kpmquockhanh/status-cube-watch/docs/superpowers/plans/2026-10-02-pomodoro-portal-ota.md

# Pomodoro card, WiFi config portal and OTA: implementation plan

> **For agentic workers:** REQUIRED SUB-SKILL: Use superpowers:subagent-driven-development (recommended) or superpowers:executing-plans to implement this plan task-by-task. Steps use checkbox (`- [ ]`) syntax for tracking.

**Goal:** Make the cube a standalone desk device: change WiFi and bridge settings from a captive portal, flash it over WiFi, and run a Pomodoro timer on it from a dedicated touch-controlled card.

**Architecture:** A new `settings` module (NVS over `config.h` defaults) feeds `net.cpp`, a blocking `portal` module (SoftAP + DNS catch-all + one-page form) and `ota` (ArduinoOTA). The Pomodoro is a pure state machine (`pomodoro.cpp`) plus a pure gesture classifier (`gesture.cpp`), both host-tested. The Pomodoro card is a virtual last card in the deck, drawn by `ui.cpp` through the existing gauge-card renderer (extended with a `RingStyle`). The bridge and payload contract are untouched.

**Tech Stack:** PlatformIO / Arduino-ESP32, LovyanGFX, ArduinoJson, `Preferences` (NVS), `WebServer` + `DNSServer`, `ArduinoOTA`; desktop sim (SDL2, `make`); plain `c++ -std=c++17` host tests.

**Spec:** `docs/superpowers/specs/2026-10-02-pomodoro-portal-ota-design.md`

## Global Constraints

- Firmware stays within C++11 (arduino-esp32's default): no default member initializers in types that are brace-initialized as aggregates, no C++14 library features. The sim and host tests build as C++17.
- Code shared with the simulator (`main.cpp`, `ui.cpp`, `payload.cpp`, `pomodoro.cpp`, `gesture.cpp`) may only use what `firmware/sim/Arduino.h` provides (`millis`, `delay`, `Serial`, `min`/`max`/`constrain`, `<cstring>`). Hardware-only code (`settings.cpp`, `portal.cpp`, `ota.cpp`) gets a sim stand-in in `firmware/sim/`.
- `pomodoro.cpp` and `gesture.cpp` take time as an argument and include no Arduino header, so host tests can build them.
- Settings precedence: NVS value if the key exists, else the `config.h` default. An empty NVS plus a working `config.h` must behave exactly as before.
- Names are fixed by the spec: OTA hostname `claude-cube`; portal AP `claude-cube-XXXX` (last two MAC bytes, upper-case hex), open, address `192.168.4.1`; NVS namespace `cube` with keys `ssid`, `pass`, `bridge`, `otapass`.
- Timings: WiFi join timeout 20 s (80 x 250 ms); boot hold for the portal 5000 ms; portal idle auto-retry 60 s; long-press 600 ms; reset-press 2000 ms; OTA/Pomodoro config constants as below.
- Pomodoro constants live in `config.h`: `POMO_FOCUS_MIN` 25, `POMO_BREAK_MIN` 5, `POMO_LONG_MIN` 15, `POMO_SESSIONS` 4. Minutes must be 1..99 and sessions 1..9 (compile-time `static_assert`). Defaults are also provided in `main.cpp` so an old `config.h` still builds.
- The Pomodoro card is the only card whose text the firmware formats (`MM:SS`). It is not in the payload, not counted against `MAX_CARDS`, and `payload.h/.cpp`, `bridge/cards.mjs` and the payload contract do not change.
- `firmware/src/config.h` is gitignored and holds real credentials: edit it only to add the new constants, never print or commit its secrets.
- This directory is **not a git repository**. Every "Commit" step below is conditional: if `git rev-parse --is-inside-work-tree` succeeds, commit; if not, skip the step (do not run `git init` unless the user asks). Commit messages end with the attribution trailer given in the session's system reminder.
- Verification commands (run from the repo root unless a `cd` is shown):
  - host tests: `cd firmware/sim && make test`
  - firmware build: `cd firmware && pio run`
  - sim build: `cd firmware/sim && make`
  - screenshots: `cd firmware/sim && make build/cube-shot && ./build/cube-shot build/shot @<view>`; open the PNG with the Read tool to look at it.

## Review Focus

Failure modes the spec implies but a straight implementation would not test. Each has a test in the task that owns the code.

1. **A long-press must not also fire a tap or swipe when the finger lifts, and a hold on a non-Pomodoro card must still be ignored on release** (Task 8: `gesture_test`).
2. **A phase must end correctly when `tick` is not called for a long time (a blocked HTTP fetch, a long gap), and when the pause press lands exactly at the end of a phase** (Task 7: `pomodoro_test`).
3. **`millis()` wraparound (about every 49 days) must not corrupt the timer or the gesture timing** (Task 7 and Task 8).
4. **Portal form safety: an SSID or bridge URL containing `"`, `<`, `&` must not break the form; a blank password keeps the stored one only while the SSID is unchanged; bridge URLs with spaces or a non-`http://` scheme are refused** (Task 1: `portal_util_test`).
5. **Bridge unreachable (WiFi fine): the deck must still contain the Pomodoro card, the timer must stay correct, and the alert must still fire** (Task 9: empty-payload shot; Task 10: manual check with a dead `BRIDGE_URL`).

---

### Task 1: Host-test harness and portal helpers

**Files:**
- Create: `firmware/sim/tests/check.h`
- Create: `firmware/sim/tests/portal_util_test.cpp`
- Create: `firmware/src/portal_util.h`
- Modify: `firmware/sim/Makefile`

**Interfaces:**
- Produces (used by Task 4): in `portal_util.h`, all `inline`, namespace-free, taking `std::string`:
  - `bool portalValidSsid(const std::string&)`: 1..32 bytes
  - `bool portalValidBridgeUrl(const std::string&)`: `http://` + non-empty host, <= 127 bytes, no whitespace
  - `std::string portalHtmlEscape(const std::string&)`
  - `std::string portalTrim(const std::string&)`
  - `std::string portalResolvePassword(oldSsid, newSsid, oldPass, newPass)`: new if non-empty; else old only when the SSID is unchanged; else empty
  - `std::string portalKeepIfBlank(old, neu)`: `neu` unless blank, then `old`
- Produces (used by Tasks 7, 8): `check.h` with `CHECK(cond)` and `int checksDone(const char *name)`; the Makefile `test` target and `TESTS` list.

- [ ] **Step 1: Write the test helper**

Create `firmware/sim/tests/check.h`:

```cpp
#pragma once
// Tiny assertion helper for the host-side tests: no framework, one include.
#include <cstdio>

static int g_checks = 0;
static int g_failed = 0;

#define CHECK(cond)                                                          \
  do {                                                                       \
    g_checks++;                                                              \
    if (!(cond)) {                                                           \
      g_failed++;                                                            \
      std::printf("  FAIL %s:%d  %s\n", __FILE__, __LINE__, #cond);          \
    }                                                                        \
  } while (0)

// Prints the summary line and returns the process exit code.
static int checksDone(const char *name) {
  std::printf("%s: %d checks, %d failed\n", name, g_checks, g_failed);
  return g_failed ? 1 : 0;
}
```

- [ ] **Step 2: Write the failing test**

Create `firmware/sim/tests/portal_util_test.cpp`:

```cpp
#include <string>

#include "check.h"
#include "portal_util.h"

namespace {

void testSsid() {
  CHECK(!portalValidSsid(""));
  CHECK(portalValidSsid("a"));
  CHECK(portalValidSsid(std::string(32, 'x')));
  CHECK(!portalValidSsid(std::string(33, 'x')));
}

void testBridgeUrl() {
  CHECK(portalValidBridgeUrl("http://192.168.1.50:8787/api/status"));
  CHECK(portalValidBridgeUrl("http://host"));
  CHECK(portalValidBridgeUrl("http://" + std::string(120, 'a')));   // 127 bytes
  CHECK(!portalValidBridgeUrl("http://" + std::string(121, 'a')));  // 128 bytes
  CHECK(!portalValidBridgeUrl(""));
  CHECK(!portalValidBridgeUrl("http://"));
  CHECK(!portalValidBridgeUrl("http://:8787/x"));
  CHECK(!portalValidBridgeUrl("http:///x"));
  CHECK(!portalValidBridgeUrl("https://host/x"));  // the bridge is plain HTTP
  CHECK(!portalValidBridgeUrl("ftp://host"));
  CHECK(!portalValidBridgeUrl("http://bad host/"));
  CHECK(!portalValidBridgeUrl("http://host/\n"));
  CHECK(!portalValidBridgeUrl("192.168.1.50:8787"));
}

void testEscape() {
  CHECK(portalHtmlEscape("plain") == "plain");
  CHECK(portalHtmlEscape("a\"b") == "a&quot;b");
  CHECK(portalHtmlEscape("<script>") == "&lt;script&gt;");
  CHECK(portalHtmlEscape("Tom & Jerry's") == "Tom &amp; Jerry&#39;s");
  CHECK(portalHtmlEscape("\"><img src=x>") == "&quot;&gt;&lt;img src=x&gt;");
  CHECK(portalHtmlEscape("") == "");
}

void testTrim() {
  CHECK(portalTrim("  http://h/ \r\n") == "http://h/");
  CHECK(portalTrim("x") == "x");
  CHECK(portalTrim("   ") == "");
  CHECK(portalTrim("") == "");
  CHECK(portalTrim(" a b ") == "a b");
}

void testPassword() {
  // A typed password always wins.
  CHECK(portalResolvePassword("home", "home", "old", "new") == "new");
  CHECK(portalResolvePassword("home", "other", "old", "new") == "new");
  // Blank keeps the stored one, but only for the same network.
  CHECK(portalResolvePassword("home", "home", "old", "") == "old");
  // A different network with a blank password is an open network.
  CHECK(portalResolvePassword("home", "cafe", "old", "") == "");
  // No stored password and a blank field stays blank.
  CHECK(portalResolvePassword("", "home", "", "") == "");
}

void testKeepIfBlank() {
  CHECK(portalKeepIfBlank("old", "") == "old");
  CHECK(portalKeepIfBlank("old", "new") == "new");
  CHECK(portalKeepIfBlank("", "") == "");
}

}  // namespace

int main() {
  testSsid();
  testBridgeUrl();
  testEscape();
  testTrim();
  testPassword();
  testKeepIfBlank();
  return checksDone("portal_util_test");
}
```

- [ ] **Step 3: Add the test target to the Makefile**

In `firmware/sim/Makefile`, replace the `.PHONY` line and add the test rules just above `clean:`. Use Edit with:

old:
```make
clean:
	rm -rf build

.PHONY: all run shot clean
```
new:
```make
# Host-side unit tests for the logic that has no hardware in it. A plain
# compiler: no SDL, LovyanGFX or Arduino. Each test links only the sources it
# is given an extra rule for below.
TESTS := build/portal_util_test

build/%_test: tests/%_test.cpp
	@mkdir -p build
	$(CXX) -std=c++17 -Wall -Wextra -I../src -Itests $(filter %.cpp,$^) -o $@

test: $(TESTS)
	@for t in $(TESTS); do ./$$t || exit 1; done

clean:
	rm -rf build

.PHONY: all run shot test clean
```

- [ ] **Step 4: Run it to verify it fails**

Run: `cd firmware/sim && make test`
Expected: FAIL to compile with `'portal_util.h' file not found`.

- [ ] **Step 5: Write the helpers**

Create `firmware/src/portal_util.h`:

```cpp
#pragma once
// Pure helpers for the setup portal. No Arduino or WiFi includes, so the host
// tests in sim/tests can build this with a plain compiler.
#include <string>

// SSIDs are 1..32 bytes. WPA passphrases are 8..63, but an open network has
// none, so the password is only length-checked where it is stored.
inline bool portalValidSsid(const std::string &s) { return !s.empty() && s.size() <= 32; }

// The bridge speaks plain HTTP on the LAN (see net.cpp). Anything else would
// only surface later as a confusing "bad BRIDGE_URL" on the display.
inline bool portalValidBridgeUrl(const std::string &u) {
  static const std::string scheme = "http://";
  if (u.size() > 127 || u.compare(0, scheme.size(), scheme) != 0) return false;
  if (u.find_first_of(" \t\r\n") != std::string::npos) return false;
  const std::string rest = u.substr(scheme.size());
  return !rest.empty() && rest[0] != ':' && rest[0] != '/';
}

// Values go back into the form as value="...", so a quote in an SSID must not
// end the attribute and a "<" must not start a tag.
inline std::string portalHtmlEscape(const std::string &in) {
  std::string out;
  out.reserve(in.size());
  for (char c : in) {
    switch (c) {
      case '&': out += "&amp;"; break;
      case '<': out += "&lt;"; break;
      case '>': out += "&gt;"; break;
      case '"': out += "&quot;"; break;
      case '\'': out += "&#39;"; break;
      default: out += c;
    }
  }
  return out;
}

inline std::string portalTrim(const std::string &s) {
  const char *ws = " \t\r\n";
  const size_t a = s.find_first_not_of(ws);
  if (a == std::string::npos) return std::string();
  return s.substr(a, s.find_last_not_of(ws) - a + 1);
}

// A blank password field means "keep what is stored", but only while the SSID
// is unchanged. Pointing the cube at a different network with a blank
// password means an open network, not the old network's password.
inline std::string portalResolvePassword(const std::string &oldSsid, const std::string &newSsid,
                                         const std::string &oldPass, const std::string &newPass) {
  if (!newPass.empty()) return newPass;
  return oldSsid == newSsid ? oldPass : std::string();
}

inline std::string portalKeepIfBlank(const std::string &oldValue, const std::string &newValue) {
  return newValue.empty() ? oldValue : newValue;
}
```

- [ ] **Step 6: Run the test to verify it passes**

Run: `cd firmware/sim && make test`
Expected: `portal_util_test: 33 checks, 0 failed` (the count may differ by a few; the point is `0 failed` and exit status 0).

- [ ] **Step 7: Commit (only if inside a git repo)**

```bash
git add firmware/sim/tests firmware/sim/Makefile firmware/src/portal_util.h
git commit -m "test: host-side test harness and portal helpers"
```

---

### Task 2: Settings (NVS) and the network layer

**Files:**
- Create: `firmware/src/settings.h`
- Create: `firmware/src/settings.cpp`
- Create: `firmware/sim/settings_sim.cpp`
- Modify: `firmware/src/net.h`, `firmware/src/net.cpp`, `firmware/sim/net_sim.cpp`
- Modify: `firmware/src/main.cpp`, `firmware/sim/Makefile`, `firmware/src/config.h.example`

**Interfaces:**
- Produces (used by Tasks 4, 5):
  - `struct Settings { char ssid[33]; char pass[64]; char bridge[128]; char otaPass[64]; }`
  - `void settingsLoad()`: call once at boot
  - `const Settings &settings()`
  - `bool settingsSave(const Settings &s)`: writes NVS and updates the in-memory copy; the caller reboots
  - `bool settingsHaveWifi()`
  - `bool netBegin()` (was `void`): `false` if not connected after about 20 s

- [ ] **Step 1: Write `settings.h`**

```cpp
#pragma once
#include <stddef.h>
#include <stdint.h>

// Everything the setup portal can change. Stored in NVS; any key that was
// never stored falls back to config.h, so a freshly flashed cube behaves
// exactly as it did before the portal existed.
struct Settings {
  char ssid[33];     // WiFi SSID, up to 32 bytes
  char pass[64];     // WPA passphrase, up to 63 bytes; empty = open network
  char bridge[128];  // bridge URL, up to 127 bytes
  char otaPass[64];  // ArduinoOTA password; empty = none
};

void settingsLoad();  // call once at boot, before anything reads settings()
const Settings &settings();
// Persists `s` and makes it the current settings. The caller reboots.
bool settingsSave(const Settings &s);
// True when there is any SSID to join, from NVS or from config.h.
bool settingsHaveWifi();
```

- [ ] **Step 2: Write `settings.cpp`**

```cpp
#include "settings.h"

#include <Arduino.h>
#include <Preferences.h>

#include "config.h"

#ifndef OTA_PASSWORD
#define OTA_PASSWORD ""
#endif

namespace {

constexpr char NS[] = "cube";
Settings g_settings;

void loadKey(Preferences &p, const char *key, char *dst, size_t cap, const char *fallback) {
  if (p.isKey(key)) {
    p.getString(key, dst, cap);
  } else {
    strlcpy(dst, fallback, cap);
  }
}

void useDefaults() {
  strlcpy(g_settings.ssid, WIFI_SSID, sizeof(g_settings.ssid));
  strlcpy(g_settings.pass, WIFI_PASSWORD, sizeof(g_settings.pass));
  strlcpy(g_settings.bridge, BRIDGE_URL, sizeof(g_settings.bridge));
  strlcpy(g_settings.otaPass, OTA_PASSWORD, sizeof(g_settings.otaPass));
}

}  // namespace

void settingsLoad() {
  Preferences p;
  // Read-write even though we only read: a read-only open of a namespace that
  // does not exist yet fails and logs an error on every first boot.
  if (!p.begin(NS, false)) {
    Serial.println("[settings] NVS unavailable -- using config.h");
    useDefaults();
    return;
  }
  loadKey(p, "ssid", g_settings.ssid, sizeof(g_settings.ssid), WIFI_SSID);
  loadKey(p, "pass", g_settings.pass, sizeof(g_settings.pass), WIFI_PASSWORD);
  loadKey(p, "bridge", g_settings.bridge, sizeof(g_settings.bridge), BRIDGE_URL);
  loadKey(p, "otapass", g_settings.otaPass, sizeof(g_settings.otaPass), OTA_PASSWORD);
  p.end();
}

const Settings &settings() { return g_settings; }

bool settingsSave(const Settings &s) {
  Preferences p;
  if (!p.begin(NS, false)) return false;
  // putString returns the byte count, which is 0 for an empty string even on
  // success, so success here just means the namespace opened. An empty value
  // is stored on purpose: a blank password means "open network", not "use the
  // config.h one".
  p.putString("ssid", s.ssid);
  p.putString("pass", s.pass);
  p.putString("bridge", s.bridge);
  p.putString("otapass", s.otaPass);
  p.end();
  g_settings = s;
  return true;
}

bool settingsHaveWifi() { return g_settings.ssid[0] != '\0'; }
```

- [ ] **Step 3: Write the sim stand-in `firmware/sim/settings_sim.cpp`**

```cpp
// Desktop stand-in for settings.cpp: a laptop has no NVS, so the simulator
// always runs on the config.h defaults and saving is a no-op.

#include <Arduino.h>

#include "../src/config.h"
#include "../src/settings.h"

#ifndef OTA_PASSWORD
#define OTA_PASSWORD ""
#endif

namespace {
Settings g_settings;
}

void settingsLoad() {
  strlcpy(g_settings.ssid, WIFI_SSID, sizeof(g_settings.ssid));
  strlcpy(g_settings.pass, WIFI_PASSWORD, sizeof(g_settings.pass));
  strlcpy(g_settings.bridge, BRIDGE_URL, sizeof(g_settings.bridge));
  strlcpy(g_settings.otaPass, OTA_PASSWORD, sizeof(g_settings.otaPass));
}

const Settings &settings() { return g_settings; }

bool settingsSave(const Settings &s) {
  g_settings = s;
  Serial.println("[settings] (sim) not persisted");
  return true;
}

bool settingsHaveWifi() { return g_settings.ssid[0] != '\0'; }
```

- [ ] **Step 4: Make `net` read from settings**

`firmware/src/net.h`: change `void netBegin();` to:

```cpp
// Joins the stored network. Returns false if it is still not connected after
// about 20 s, so the caller can fall back to the setup portal.
bool netBegin();
```

`firmware/src/net.cpp`: replace `#include "config.h"` with `#include "settings.h"`. Replace the whole `netBegin` function with:

```cpp
bool netBegin() {
  WiFi.mode(WIFI_STA);
  WiFi.setSleep(true);  // the radio idles between 5s polls
  const Settings &s = settings();
  // A null passphrase is how the WiFi library spells "open network".
  WiFi.begin(s.ssid, s.pass[0] ? s.pass : nullptr);
  Serial.printf("[net] connecting to %s", s.ssid);
  for (int i = 0; i < 80 && WiFi.status() != WL_CONNECTED; i++) {
    delay(250);
    Serial.print('.');
  }
  Serial.println();
  if (WiFi.status() == WL_CONNECTED) {
    Serial.printf("[net] %s  rssi %d\n", WiFi.localIP().toString().c_str(), WiFi.RSSI());
    return true;
  }
  fail("wifi timeout");
  Serial.println("[net] could not join");
  return false;
}
```

and change `http.begin(BRIDGE_URL)` to `http.begin(settings().bridge)`.

`firmware/sim/net_sim.cpp`: change `void netBegin() {` to `bool netBegin() {` and add `return true;` as its last line:

```cpp
bool netBegin() {
  Serial.printf("[net] simulator -> %s\n", bridgeUrl().c_str());
  return true;
}
```

- [ ] **Step 5: Use settings in `main.cpp`**

Edits in `firmware/src/main.cpp`:
1. After `#include "payload.h"` add `#include "settings.h"`.
2. In `setup()`, after `Serial.println("\n[boot] claude-status-cube");` add `settingsLoad();`.
3. Replace `uiMessage(lcd, "CONNECTING", WIFI_SSID);` with `uiMessage(lcd, "CONNECTING", settings().ssid);`.

(`netBegin();` stays as a bare call for now; Task 4 uses its result.)

- [ ] **Step 6: Wire the sim Makefile and document the config**

In `firmware/sim/Makefile` change:

```make
SRCS := ../src/main.cpp ../src/ui.cpp ../src/payload.cpp \
        net_sim.cpp touch_sim.cpp sdl_main.cpp
```
to:
```make
SRCS := ../src/main.cpp ../src/ui.cpp ../src/payload.cpp \
        net_sim.cpp touch_sim.cpp settings_sim.cpp sdl_main.cpp
```

Append to `firmware/src/config.h.example`:

```c
// Optional: default OTA password. The setup portal can set or change it; with
// neither, OTA still works but anyone on the network can flash the cube.
// #define OTA_PASSWORD  "choose-one"
```

- [ ] **Step 7: Build everything**

Run: `cd firmware && pio run`
Expected: `[SUCCESS]`.

Run: `cd firmware/sim && make`
Expected: `built build/cube-sim` with no errors.

Behaviour is unchanged at this point: with an empty NVS, `settings()` returns the `config.h` values.

- [ ] **Step 8: Commit (only if inside a git repo)**

```bash
git add firmware/src firmware/sim
git commit -m "feat(firmware): NVS-backed settings with config.h fallback"
```

---
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
