kpmquockhanh/status-cube-watch/firmware/src/readings_key.h

#pragma once
// What the cards read, folded into one number, for screen sleep: main.cpp
// counts a payload as activity (idle_sleep.h) only when its key differs from
// the last one's. "A payload arrived" is not enough: the Mac resends the same
// payload every 5 s and the bridge rebuilds it for every WiFi poll, so the
// screen would stay on for as long as the link is up. Pure, so it is
// host-tested.
//
// In the key: the card count, titles, every gauge, the mail badge, and a text
// card's value (spend, tokens, model), which move only when Claude is used.
// Left out: a ring card's value, which is the reset countdown, and every
// sub-line and legend row, which carry countdowns, projections and "active 3m
// ago". All of those change with the clock alone and would keep the screen
// awake. Accents follow the gauges, so they add nothing.

#include <stddef.h>
#include <stdint.h>

#include "payload.h"

namespace readings_detail {
inline uint32_t mix(uint32_t h, uint8_t b) { return (h ^ b) * 16777619u; }  // FNV-1a

inline uint32_t mixStr(uint32_t h, const char *s, size_t cap) {
  for (size_t i = 0; i < cap && s[i]; i++) h = mix(h, (uint8_t)s[i]);
  return mix(h, 0);  // so "AB" + "C" and "A" + "BC" differ
}
}  // namespace readings_detail

inline uint32_t readingsKey(const Payload &p) {
  using namespace readings_detail;
  uint32_t h = 2166136261u;
  h = mix(h, p.valid);
  h = mix(h, p.nCards);
  for (uint8_t i = 0; i < p.nCards && i < MAX_CARDS; i++) {
    const Card &c = p.cards[i];
    h = mixStr(h, c.title, sizeof(c.title));
    h = mix(h, (uint8_t)c.gauge);
    h = mix(h, (uint8_t)c.gauge2);
    if (c.gauge == GAUGE_NONE) h = mixStr(h, c.value, sizeof(c.value));
    h = mixStr(h, c.mail, sizeof(c.mail));
  }
  return h;
}
