kpmquockhanh/status-cube-watch/firmware/src/portal_util.h

#pragma once
// Pure helpers for the setup portal. No Arduino or WiFi includes, so the host
// tests in sim/tests can build this with a plain compiler.
#include <string>

// Reboot into the normal boot flow only when a Mac becomes bonded while the
// portal is up. An already-bonded cube reaching the portal (boot-time hold) must
// stay there so it can use "Forget paired Mac".
inline bool portalBondedTransition(bool bondedAtStart, bool bondedNow) { return !bondedAtStart && bondedNow; }

// The portal runs AP+STA, so the station side can rejoin the saved network
// while the form is up. A join that fails makes the radio scan every channel,
// and the SoftAP has to follow it, which knocks a phone off the form and starves
// a Bluetooth pairing. So the core's auto-reconnect is off in the portal, and
// this decides when to make one bounded attempt: only while `quiet` (no phone on
// the AP, no Mac pairing), at most ATTEMPT_MS long, one every
// EVERY_MS. A joined station is never stopped: it stays on one channel and does
// not disturb the AP. Unsigned arithmetic: correct across a millis() wrap.
enum class PortalStaAction : unsigned char { None, Begin, Stop };

class PortalSta {
 public:
  static constexpr unsigned long ATTEMPT_MS = 10000;  // a join plus DHCP
  static constexpr unsigned long EVERY_MS = 30000;    // from one attempt's start to the next

  // `tryNow`: the first attempt may start at once (the portal was asked for),
  // else a full period from now (a join has just failed).
  void begin(unsigned long now, bool tryNow) {
    _trying = false;
    _up = false;
    _start = tryNow ? now - EVERY_MS : now;
  }

  PortalStaAction update(unsigned long now, bool haveSsid, bool quiet, bool staUp) {
    if (staUp) {
      _up = true;
      _trying = false;
      return PortalStaAction::None;
    }
    if (_up) {  // the link dropped: try again as soon as it is quiet
      _up = false;
      _start = now - EVERY_MS;
    }
    if (_trying) {
      if (quiet && now - _start < ATTEMPT_MS) return PortalStaAction::None;
      _trying = false;
      return PortalStaAction::Stop;
    }
    if (!haveSsid || !quiet || now - _start < EVERY_MS) return PortalStaAction::None;
    _trying = true;
    _start = now;
    return PortalStaAction::Begin;
  }

 private:
  bool _trying = false;
  bool _up = false;
  unsigned long _start = 0;
};

// A cube that reached the portal only because its WiFi was down goes back to
// the normal boot flow as soon as the saved network is joined, but never while
// someone is using the form or a Mac is pairing.
inline bool portalStaRecoveredReboot(bool autoRetry, bool staUp, bool phoneOnAp, bool bleBusy) {
  return autoRetry && staUp && !phoneOnAp && !bleBusy;
}

// With AP+STA the form is also reachable from the LAN. A request must name the
// cube by the address it arrived on (a DNS-rebinding page names its own host)
// and a POST must carry the token that only the served form holds (another
// page on the LAN cannot read it, so it cannot forge a save or a forget).
inline bool portalHostIs(const std::string &host, const std::string &ip) {
  return host == ip || host == ip + ":80";
}

inline bool portalTokenOk(const std::string &sent, const std::string &token) {
  return !token.empty() && sent == token;
}

// SSIDs are 1..32 bytes. WPA passphrases are 8..63, but an open network has
// none, so the password is only length-checked where it is stored.
inline bool portalValidSsid(const std::string &s) { return !s.empty() && s.size() <= 32; }

// WPA passphrases are 8..63 characters; WiFi.begin rejects anything shorter, so
// storing one would leave the cube retrying a join that cannot succeed. Empty
// means an open network.
inline bool portalValidWifiPassword(const std::string &p) {
  return p.empty() || (p.size() >= 8 && p.size() <= 63);
}

// The bridge speaks plain HTTP on the LAN (see net.cpp). Anything else would
// only surface later as a confusing "bad BRIDGE_URL" on the display.
inline bool portalValidBridgeUrl(const std::string &u) {
  static const std::string scheme = "http://";
  if (u.size() > 127 || u.compare(0, scheme.size(), scheme) != 0) return false;
  if (u.find_first_of(" \t\r\n") != std::string::npos) return false;
  const std::string rest = u.substr(scheme.size());
  return !rest.empty() && rest[0] != ':' && rest[0] != '/';
}

// Values go back into the form as value="...", so a quote in an SSID must not
// end the attribute and a "<" must not start a tag.
inline std::string portalHtmlEscape(const std::string &in) {
  std::string out;
  out.reserve(in.size());
  for (char c : in) {
    switch (c) {
      case '&': out += "&amp;"; break;
      case '<': out += "&lt;"; break;
      case '>': out += "&gt;"; break;
      case '"': out += "&quot;"; break;
      case '\'': out += "&#39;"; break;
      default: out += c;
    }
  }
  return out;
}

inline std::string portalTrim(const std::string &s) {
  const char *ws = " \t\r\n";
  const size_t a = s.find_first_not_of(ws);
  if (a == std::string::npos) return std::string();
  return s.substr(a, s.find_last_not_of(ws) - a + 1);
}

// A blank password field means "keep what is stored", but only while the SSID
// is unchanged. Pointing the cube at a different network with a blank
// password means an open network, not the old network's password.
inline std::string portalResolvePassword(const std::string &oldSsid, const std::string &newSsid,
                                         const std::string &oldPass, const std::string &newPass) {
  if (!newPass.empty()) return newPass;
  return oldSsid == newSsid ? oldPass : std::string();
}

inline std::string portalKeepIfBlank(const std::string &oldValue, const std::string &newValue) {
  return newValue.empty() ? oldValue : newValue;
}

// A blank OTA password field keeps the stored one, so clearing it takes the
// form's "remove" box.
inline std::string portalOtaPassword(const std::string &oldPass, const std::string &typed, bool clear) {
  return clear ? std::string() : portalKeepIfBlank(oldPass, typed);
}

// Parses a whole-string decimal integer in [lo, hi]. A blank field keeps
// `keep`; anything else (letters, trailing junk, out of range) is rejected.
inline bool portalParseInt(const std::string &raw, int lo, int hi, int keep, int &out) {
  const std::string t = portalTrim(raw);
  if (t.empty()) { out = keep; return true; }
  if (t.size() > 4) return false;
  int v = 0;
  for (char c : t) {
    if (c < '0' || c > '9') return false;
    v = v * 10 + (c - '0');
  }
  if (v < lo || v > hi) return false;
  out = v;
  return true;
}
