kpmquockhanh/status-cube-watch/firmware/sim/Arduino.h

#pragma once
// Just enough of the Arduino core for the desktop simulator.
//
// This is deliberately tiny: the firmware sources only reach for millis(),
// delay(), Serial logging and the clamp helpers. Everything here is an inline
// function rather than a macro so it cannot collide with <algorithm> or with
// LovyanGFX's own templates.

#include <chrono>
#include <cstdarg>
#include <cstdint>
#include <cstdlib>
#include <cstdio>
#include <cstring>
#include <thread>

#ifdef SIM_VIRTUAL_CLOCK
// `make bench`: time is a counter that sim/bench.cpp advances. A ten-minute
// scenario runs in about a second, and every run gives the same result. A
// delay is booked as time the CPU spends idle, at the clock it was set to.
extern uint64_t g_simUs;
void simDelayUs(uint64_t us);
void simSetCpuMhz(uint32_t mhz);
inline uint32_t millis() { return (uint32_t)(g_simUs / 1000); }
inline void delay(uint32_t ms) { simDelayUs(ms * 1000ull); }
inline bool setCpuFrequencyMhz(uint32_t mhz) {
  simSetCpuMhz(mhz);
  return true;
}
#else
inline uint32_t millis() {
  using namespace std::chrono;
  static const auto t0 = steady_clock::now();
  return (uint32_t)duration_cast<milliseconds>(steady_clock::now() - t0).count();
}

inline void delay(uint32_t ms) { std::this_thread::sleep_for(std::chrono::milliseconds(ms)); }
inline bool setCpuFrequencyMhz(uint32_t) { return true; }  // no-op on the desktop
#endif

struct EspShim {
  [[noreturn]] void restart() { std::printf("[esp] restart requested (sim exits)\n"); std::exit(0); }
};
inline EspShim ESP;

inline int max(int a, int b) { return a > b ? a : b; }
inline int min(int a, int b) { return a < b ? a : b; }
inline int constrain(int v, int lo, int hi) { return v < lo ? lo : (v > hi ? hi : v); }

// Serial goes to the terminal, so the simulator prints the same boot and
// fetch diagnostics you would see over USB.
struct SerialShim {
  void begin(unsigned long) {}
  void print(char c) { fputc(c, stdout); fflush(stdout); }
  void print(const char *s) { fputs(s, stdout); fflush(stdout); }
  void println() { fputc('\n', stdout); }
  void println(const char *s) { printf("%s\n", s); }
  int printf(const char *fmt, ...) {
    va_list ap;
    va_start(ap, fmt);
    const int n = vfprintf(stdout, fmt, ap);
    va_end(ap);
    fflush(stdout);
    return n;
  }
};
inline SerialShim Serial;
